Skidude88/Skidude88-G29-PS4-LoadCell-Arduino/img/150duty_245Hz.bmp

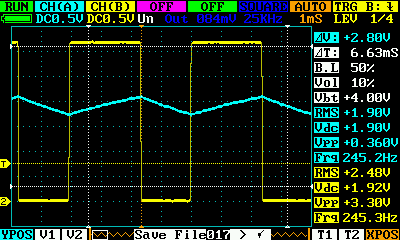
img/150duty_245Hz.bmp
