Skidude88/Skidude88-G29-PS4-LoadCell-Arduino/img/Arduino-G29Pedal2.jpg

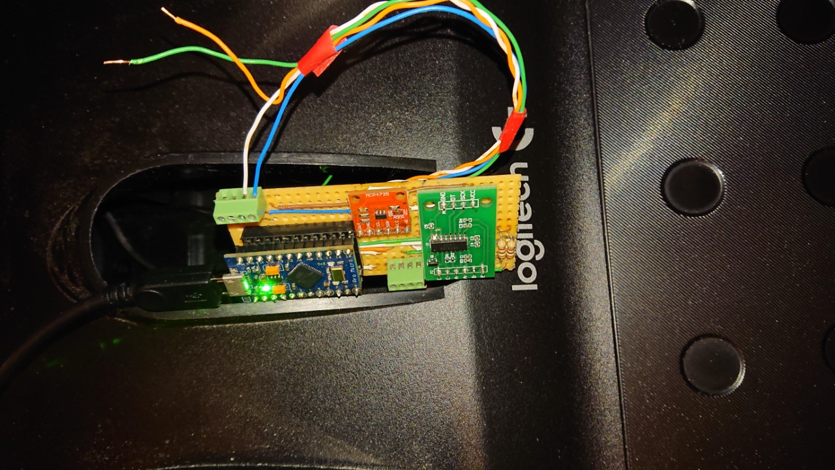
img/Arduino-G29Pedal2.jpg
