Skidude88/Skidude88-G29-PS4-LoadCell-Arduino/img/Cover1.jpg

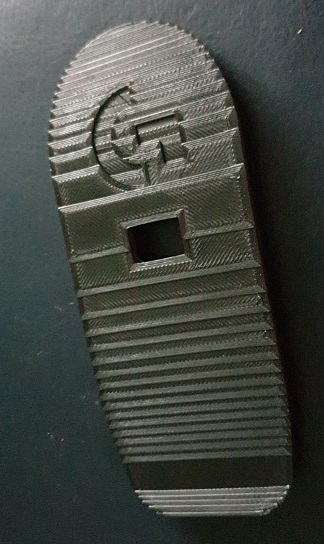
img/Cover1.jpg
