Skidude88/Skidude88-G29-PS4-LoadCell-Arduino/img/Cover2.JPG

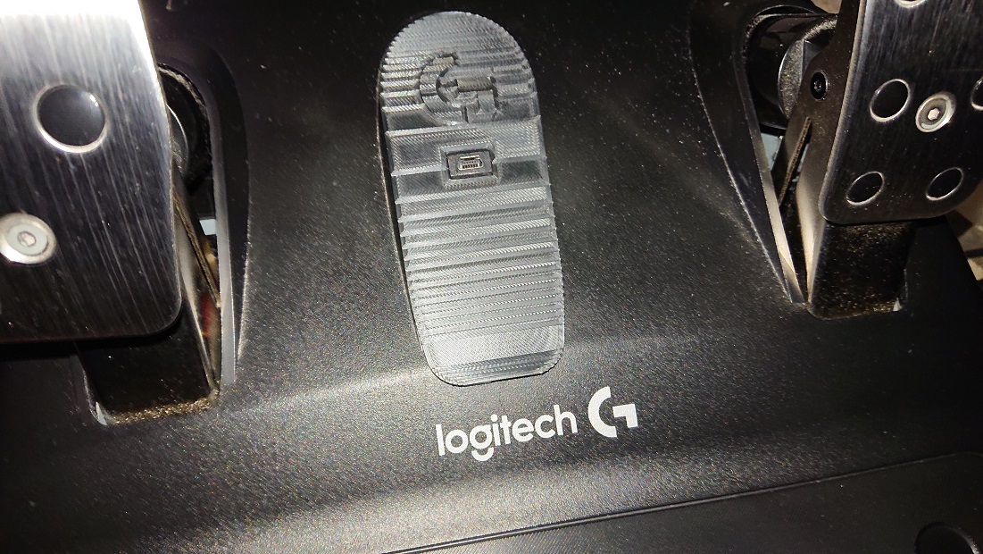
img/Cover2.JPG
