Skidude88/Skidude88-G29-PS4-LoadCell-Arduino/img/Final data analysis.JPG

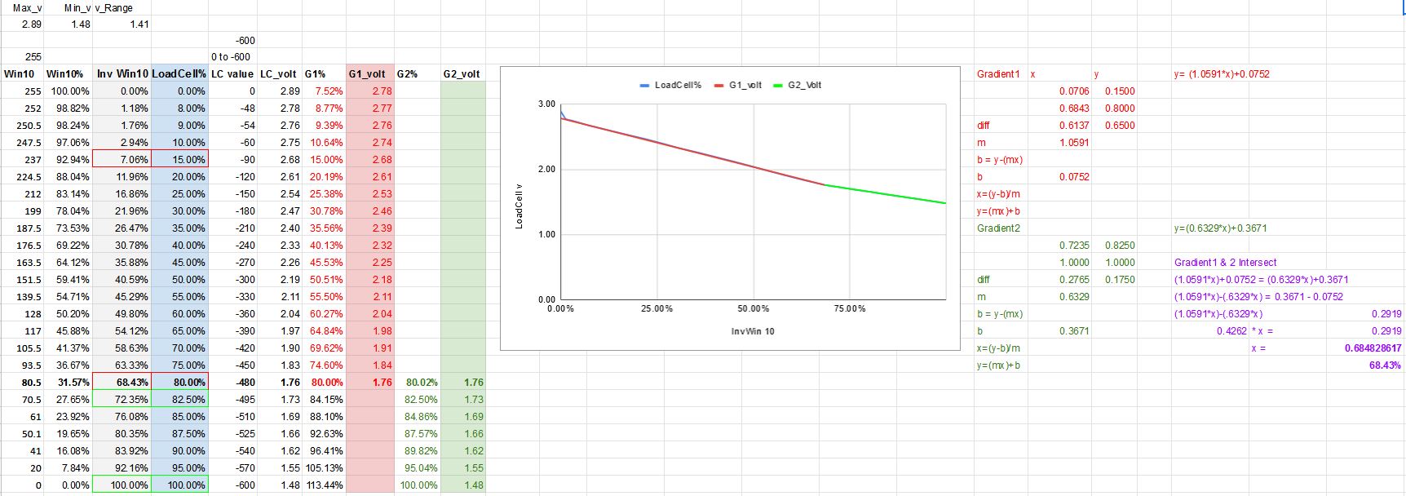
img/Final data analysis.JPG
