Skidude88/Skidude88-G29-PS4-LoadCell-Arduino/img/Final Gradients.JPG

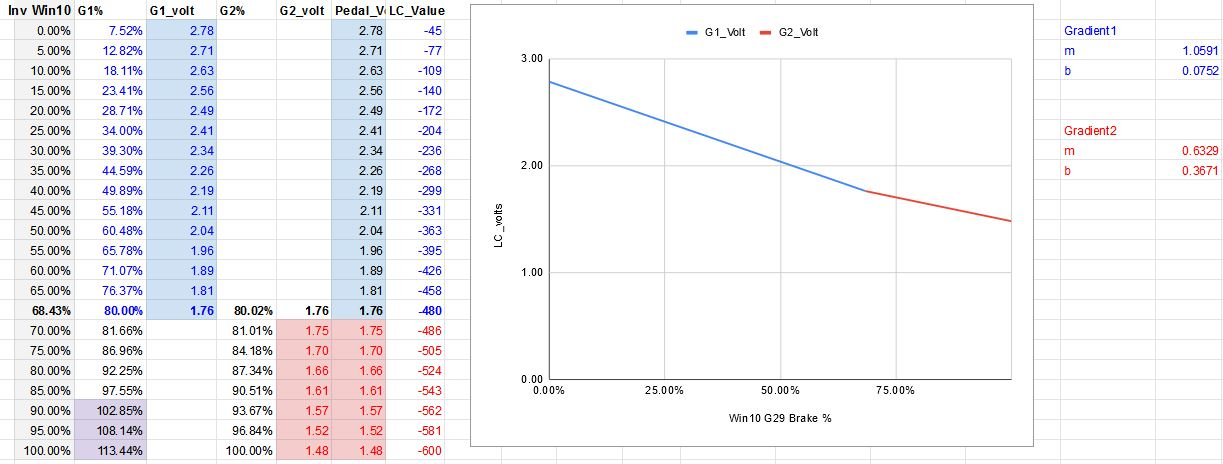
img/Final Gradients.JPG
