Skidude88/Skidude88-G29-PS4-LoadCell-Arduino/img/Final PCB.JPG

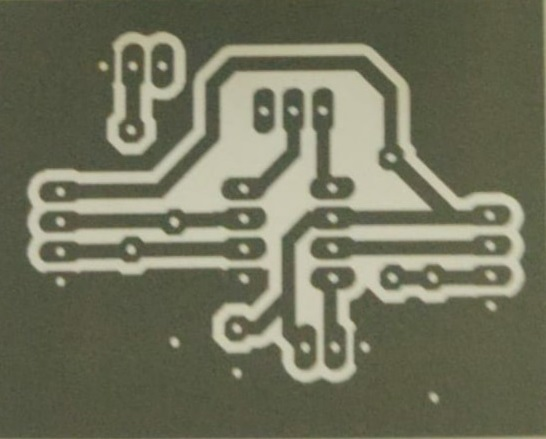
img/Final PCB.JPG
