Skidude88/Skidude88-G29-PS4-LoadCell-Arduino/img/G-Hub.png

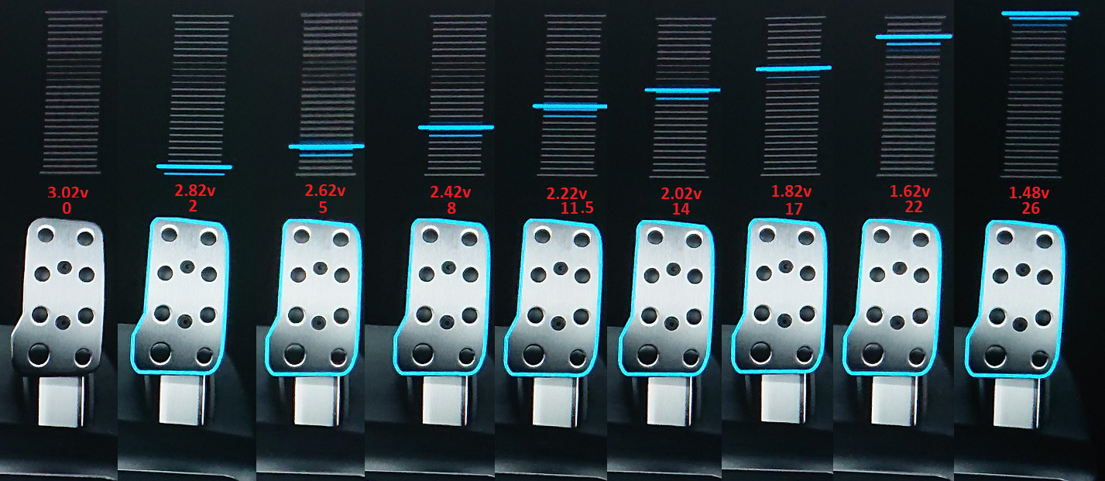
img/G-Hub.png
