Skidude88/Skidude88-G29-PS4-LoadCell-Arduino/img/GraphReader-Linear Plot.JPG

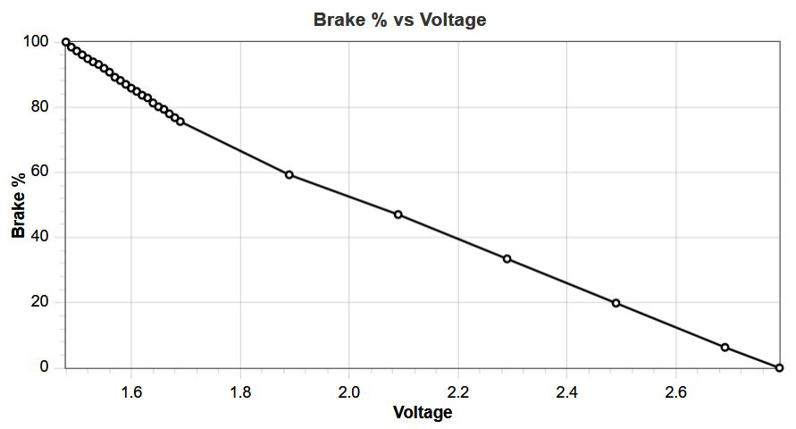
img/GraphReader-Linear Plot.JPG
