Skidude88/Skidude88-G29-PS4-LoadCell-Arduino/img/HX711.JPG

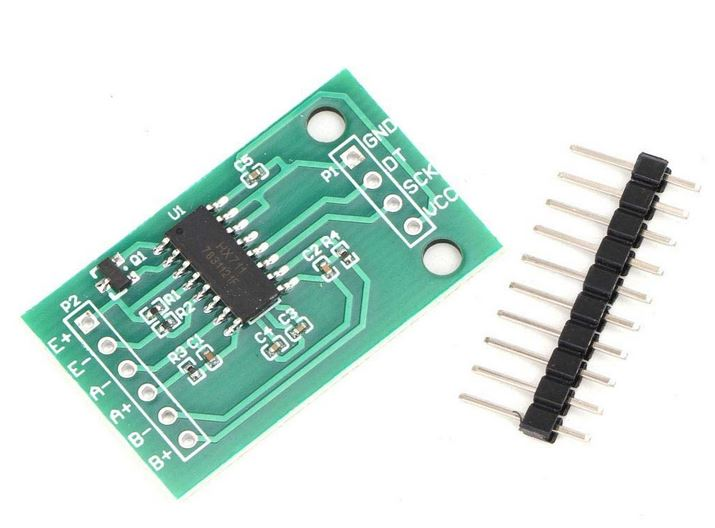
img/HX711.JPG
