Skidude88/Skidude88-G29-PS4-LoadCell-Arduino/img/LC_vs_G29WIn10.JPG

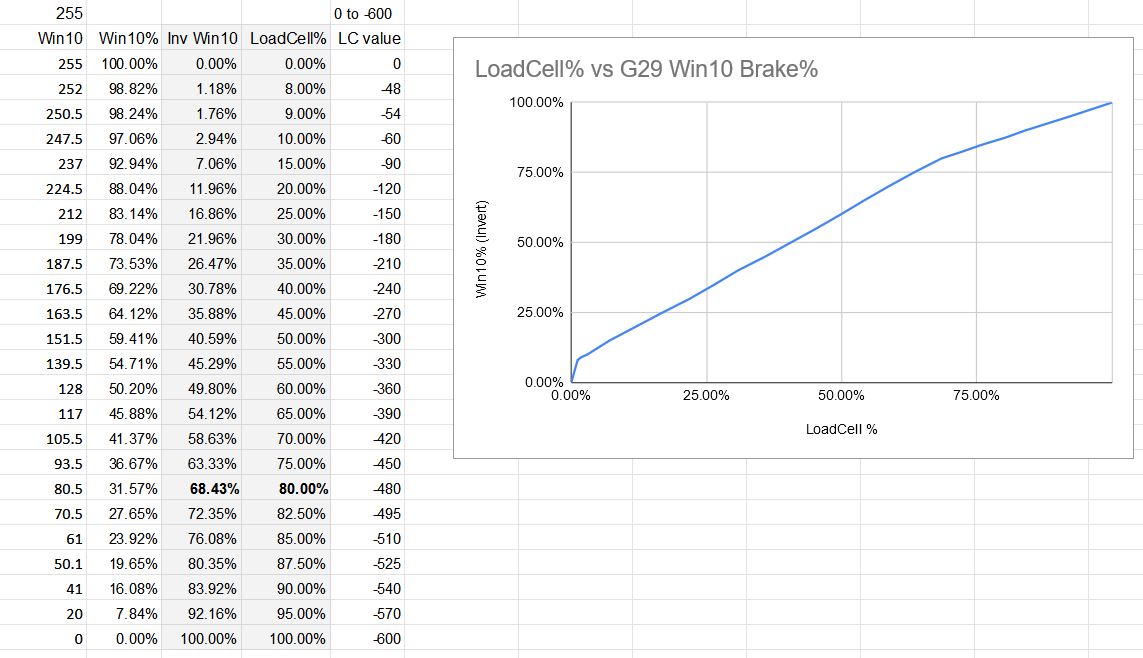
img/LC_vs_G29WIn10.JPG
