Skidude88/Skidude88-G29-PS4-LoadCell-Arduino/img/MCP4725.JPG

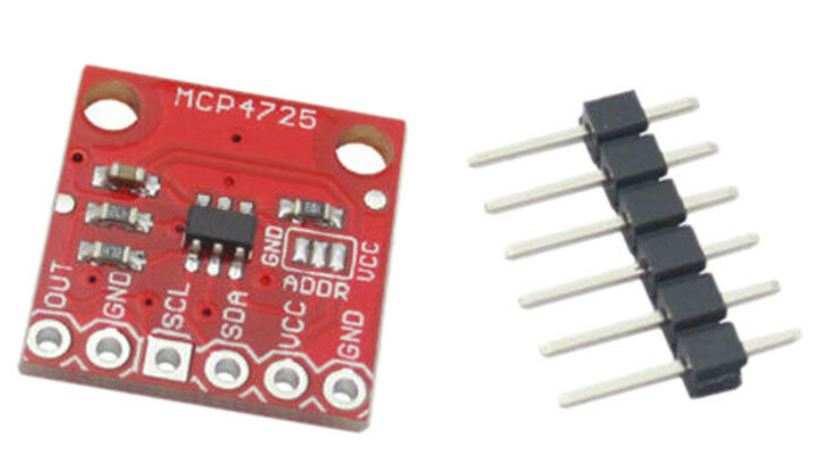
img/MCP4725.JPG
