Skidude88/Skidude88-G29-PS4-LoadCell-Arduino/img/New Gradient-intesect workings.JPG

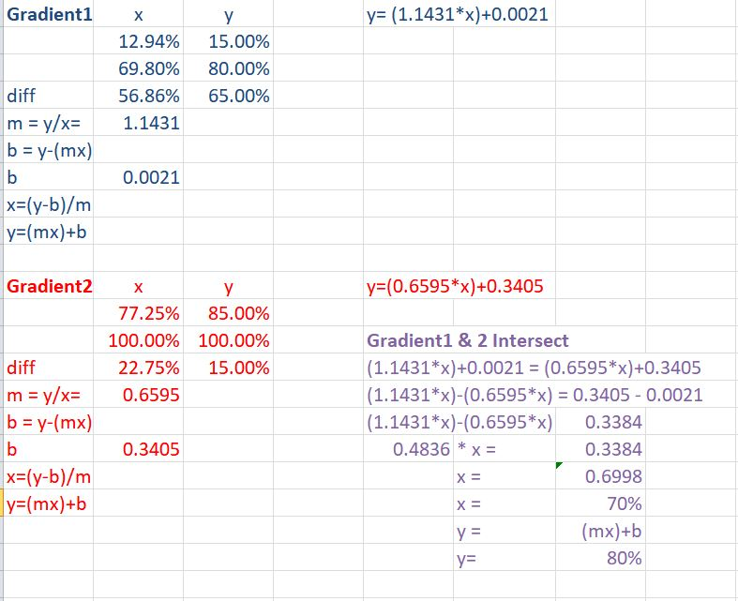
img/New Gradient-intesect workings.JPG
