Skidude88/Skidude88-G29-PS4-LoadCell-Arduino/img/New_Table.JPG

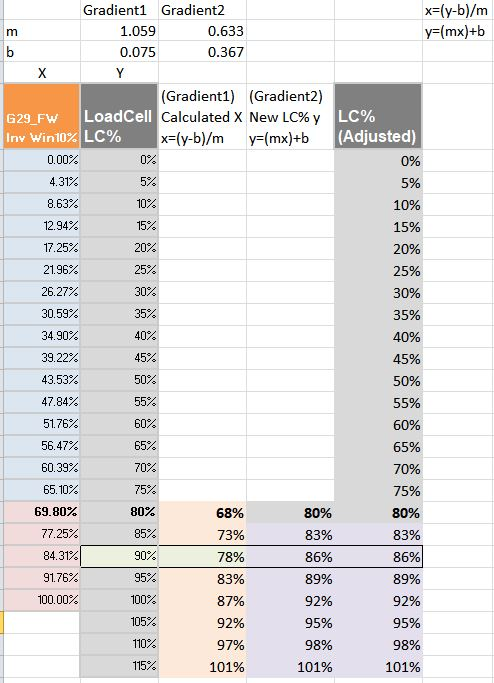
img/New_Table.JPG
