Skidude88/Skidude88-G29-PS4-LoadCell-Arduino/img/Pedal Analogue s.jpg

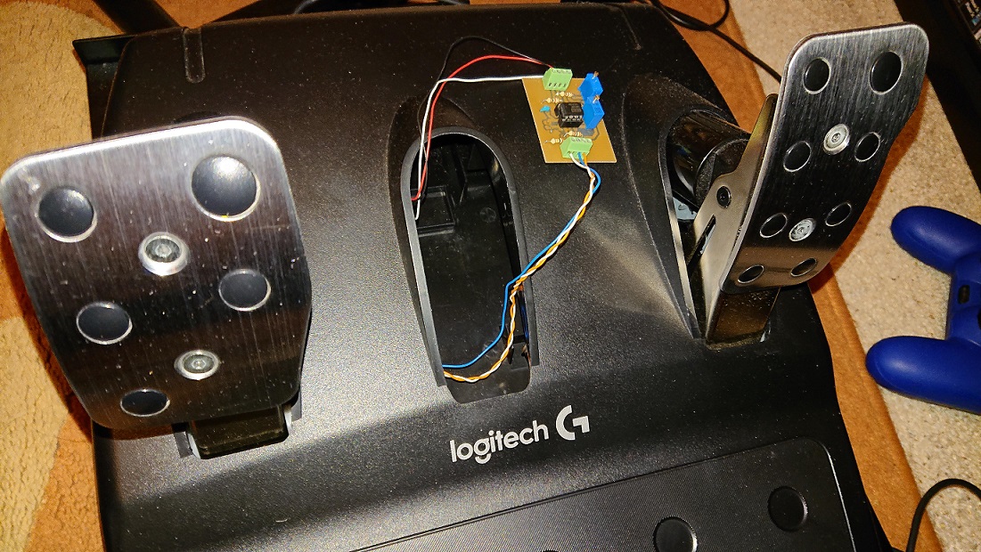
img/Pedal Analogue s.jpg
