Skidude88/Skidude88-G29-PS4-LoadCell-Arduino/img/Pedal Digital s.jpg

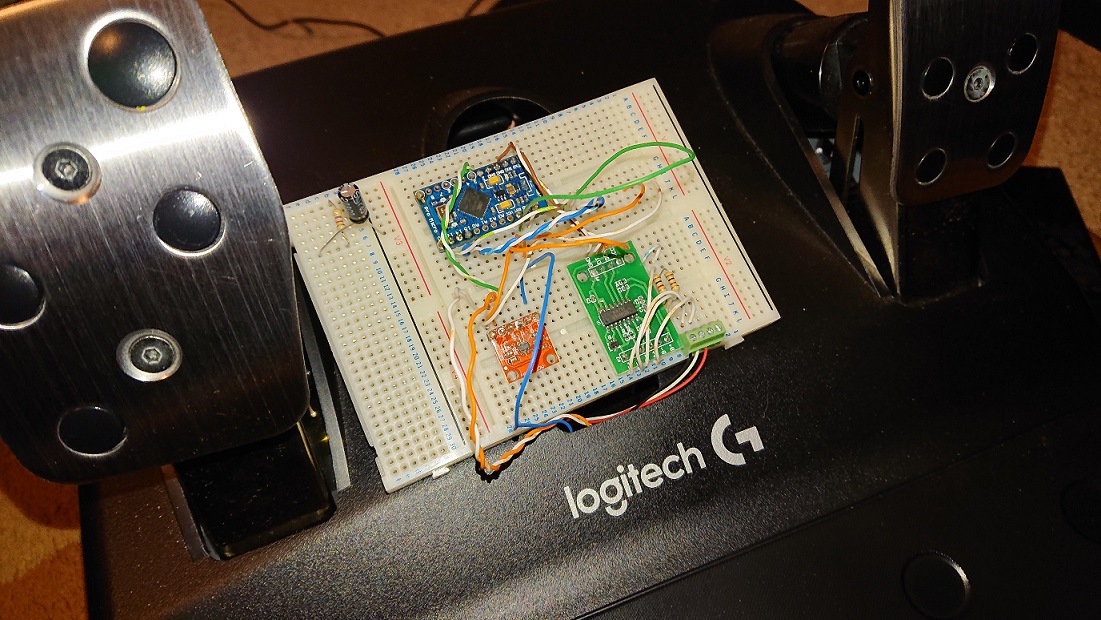
img/Pedal Digital s.jpg
