Skidude88/Skidude88-G29-PS4-LoadCell-Arduino/img/Project Board b.jpg

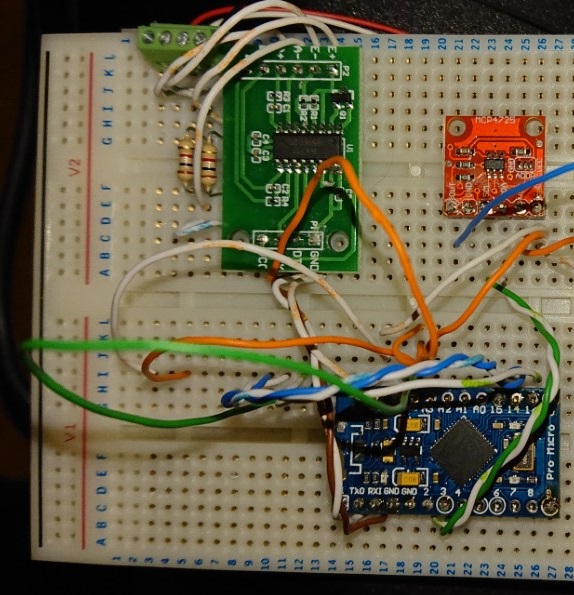
img/Project Board b.jpg
