Skidude88/Skidude88-G29-PS4-LoadCell-Arduino/img/Project Board with IPS a.jpg

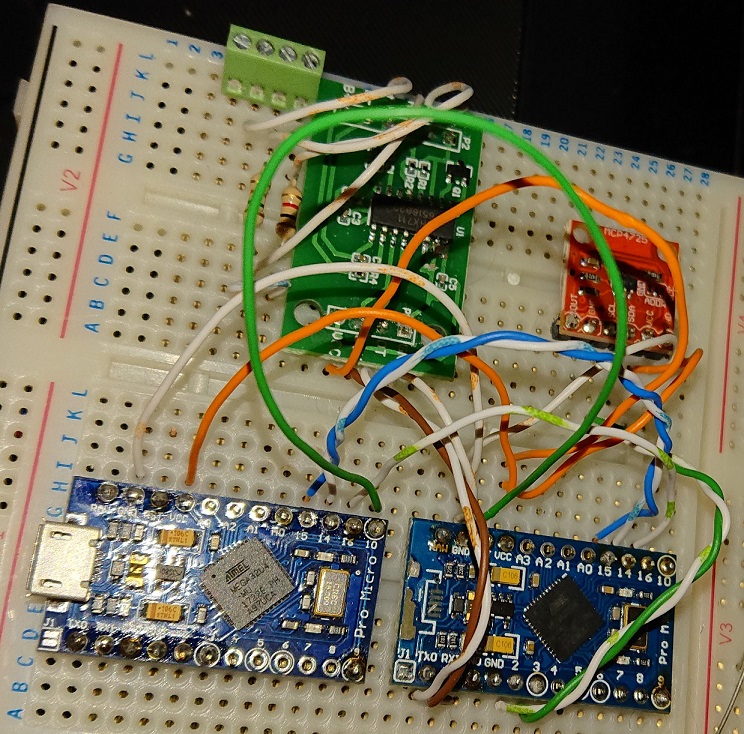
img/Project Board with IPS a.jpg
