Skidude88/Skidude88-G29-PS4-LoadCell-Arduino/img/ProMicro-HX711-MCP4725DAC-Double.png

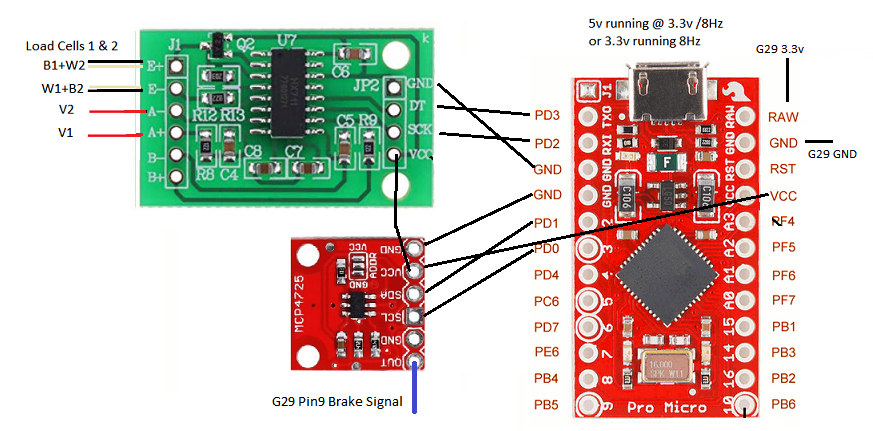
img/ProMicro-HX711-MCP4725DAC-Double.png
