Skidude88/Skidude88-G29-PS4-LoadCell-Arduino/img/Proto Board Underside (Flipped).jpg

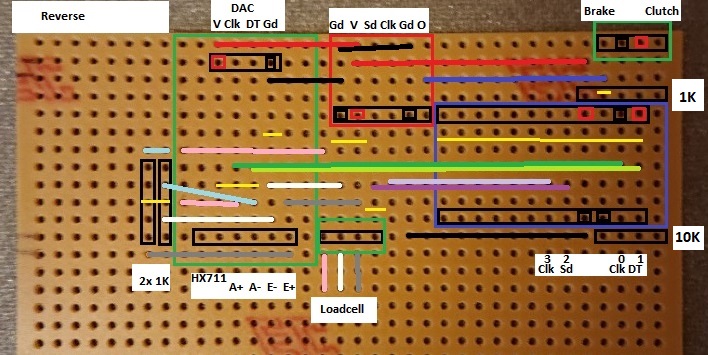
img/Proto Board Underside (Flipped).jpg
