Skidude88/Skidude88-G29-PS4-LoadCell-Arduino/img/Proto Board.jpg

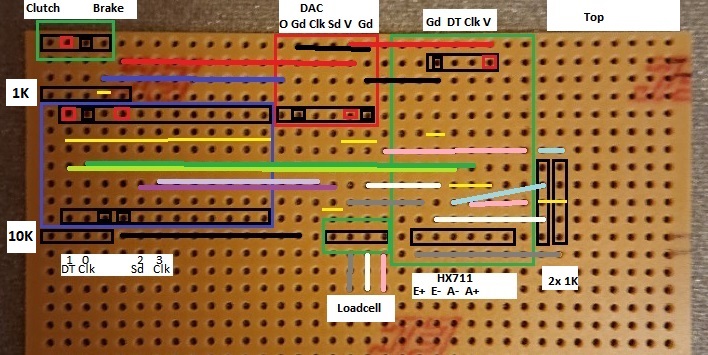
img/Proto Board.jpg
