Skidude88/Skidude88-G29-PS4-LoadCell-Arduino/img/Serial Port Plot.JPG

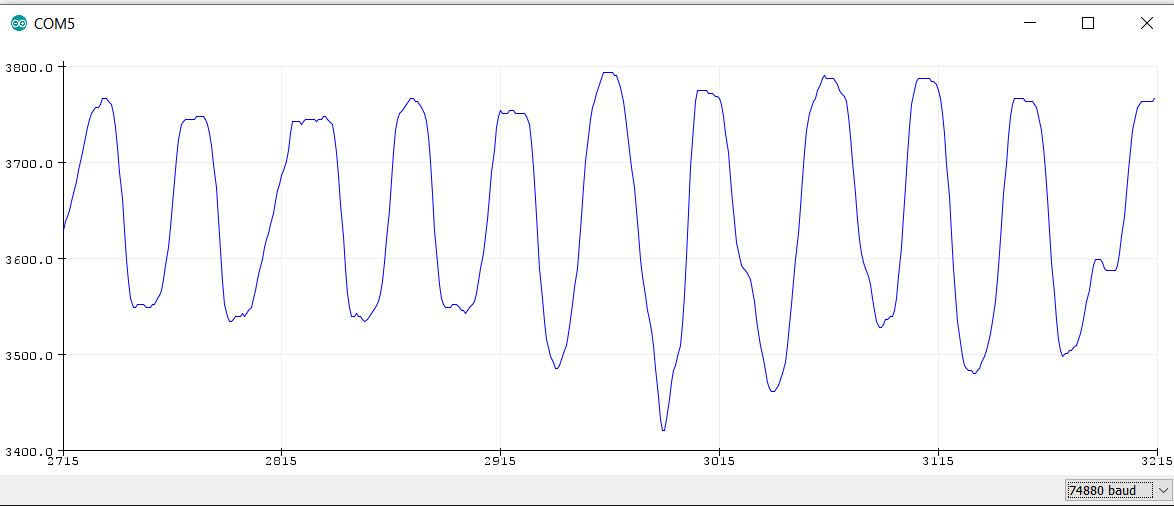
img/Serial Port Plot.JPG
