Skidude88/Skidude88-G29-PS4-LoadCell-Arduino/img/USB2 Extender.jpg

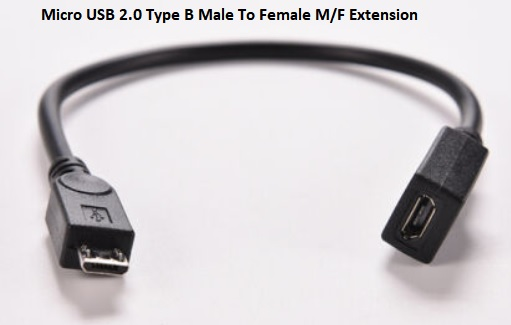
img/USB2 Extender.jpg
