Skidude88/Skidude88-G29-PS4-LoadCell-Arduino/img/Calibration summary.JPG

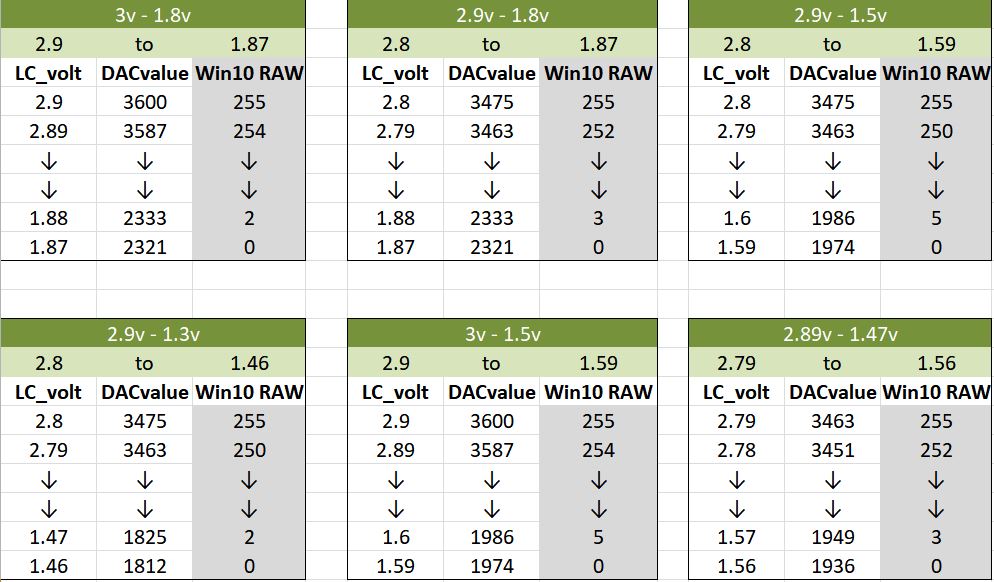
img/Calibration summary.JPG
