Skidude88/Skidude88-G29-PS4-LoadCell-Arduino/img/DiView Results.JPG

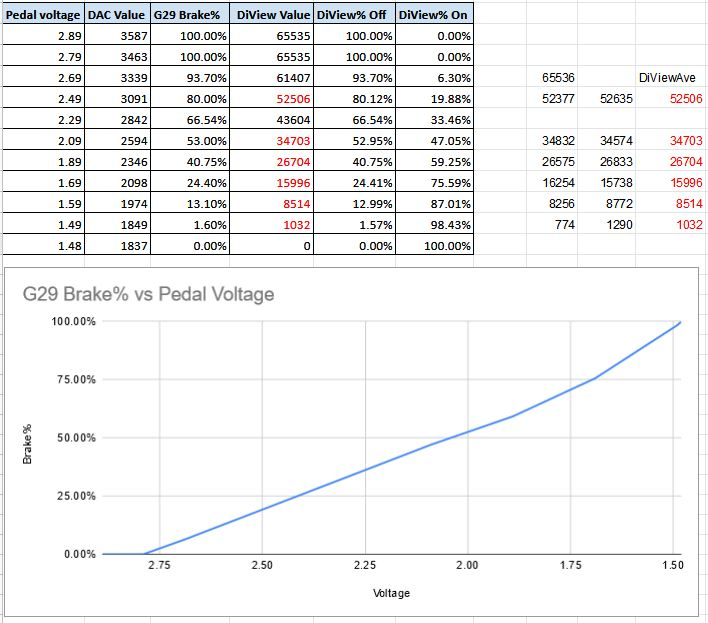
img/DiView Results.JPG
