Skidude88/Skidude88-G29-PS4-LoadCell-Arduino/pcb/load_cell_amp_JA.sch

## EAGLE design pcb/load_cell_amp_JA.sch (2020-01-09)

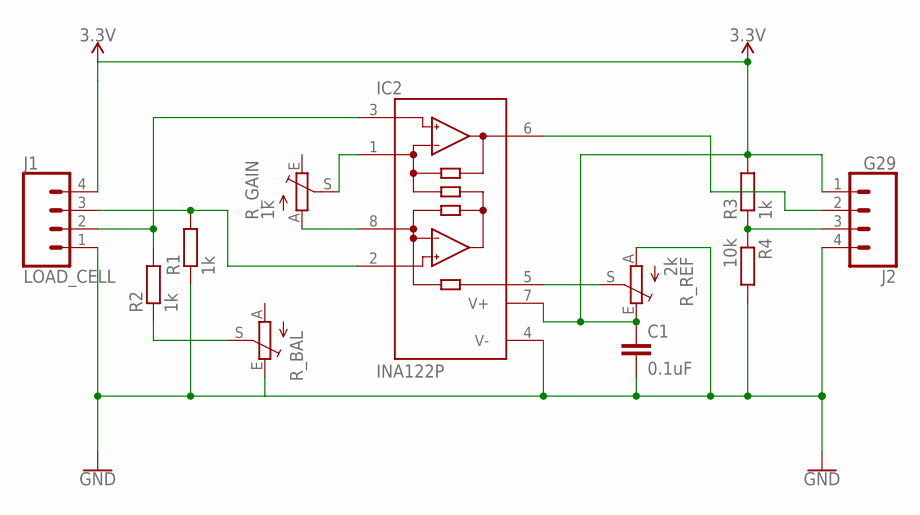
[picture p35: schematic load_cell_amp_JA.sch]

Parts:
C1: 0.1uF; C025-024X044
IC2: INA122P; DIL08
J1: LOAD_CELL; 04P
J2: G29; 04P
R1, R2, R3: 1k; 0207/10
R4: 10k; 0207/10
R_BAL: 10; RJ9W
R_GAIN: 1k; RJ9W
R_REF: 2k; RJ9W

Connections:
3.3V: C1.1, IC2.7 (V+), J1.4, J2.1, R3.2, R_REF.E
GND: C1.2, IC2.4 (V-), J1.1, J2.4, R1.1, R4.2, R_BAL.E, R_REF.A
unnamed: IC2.2 (-IN), J1.3, R1.2
unnamed: IC2.3 (+IN), J1.2, R2.2
unnamed: R2.1, R_BAL.S
unnamed: IC2.1 (RG), R_GAIN.S
unnamed: IC2.8 (RG), R_GAIN.A
unnamed: J2.3, R3.1, R4.1
unnamed: IC2.6 (OUT), J2.2
unnamed: IC2.5 (REF), R_REF.S
